guidobonerz/snatchfreezer/docs/2019-03-17 18_59_53-Snatchfreezer.png

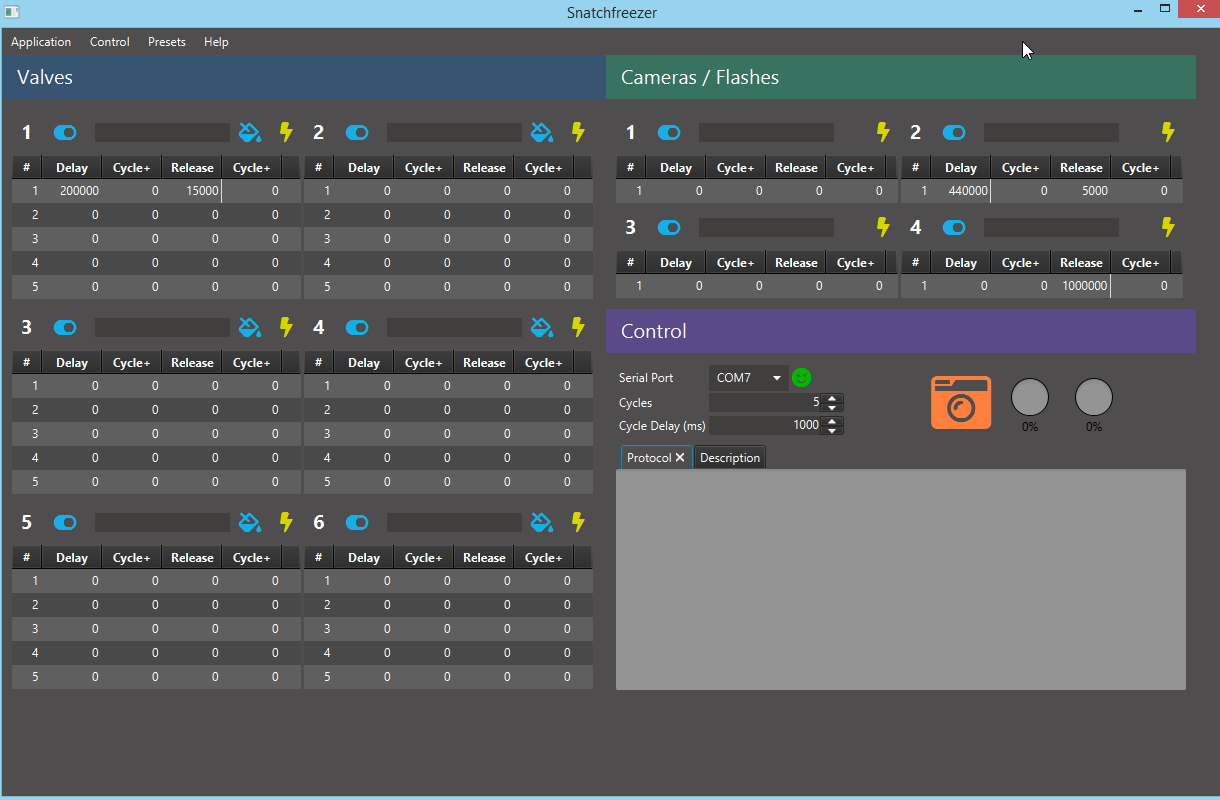
docs/2019-03-17 18_59_53-Snatchfreezer.png
